vladantrhlik/VT-40/img/2.jpg

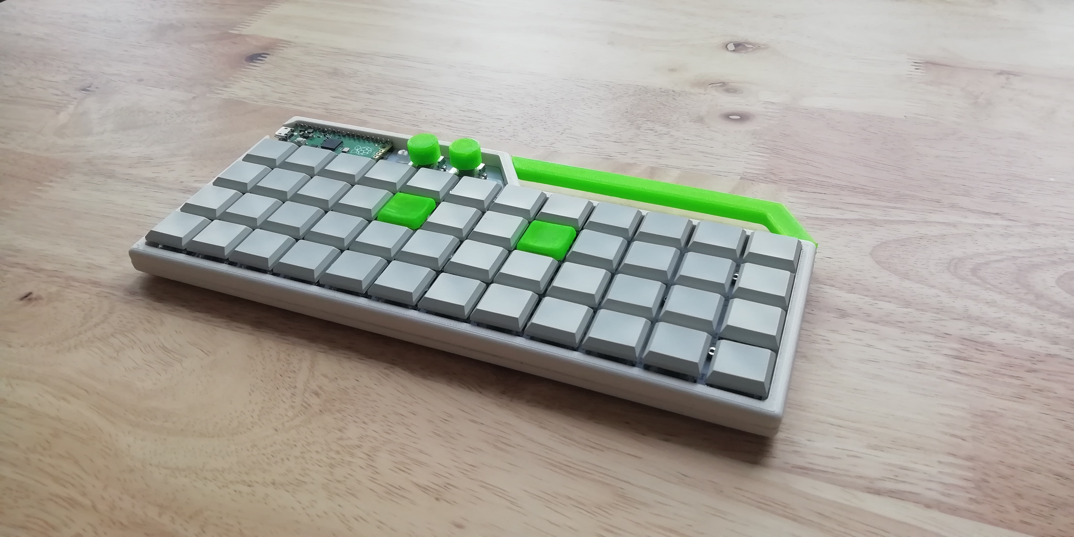
img/2.jpg
