vladantrhlik/VT-40/img/3.jpg

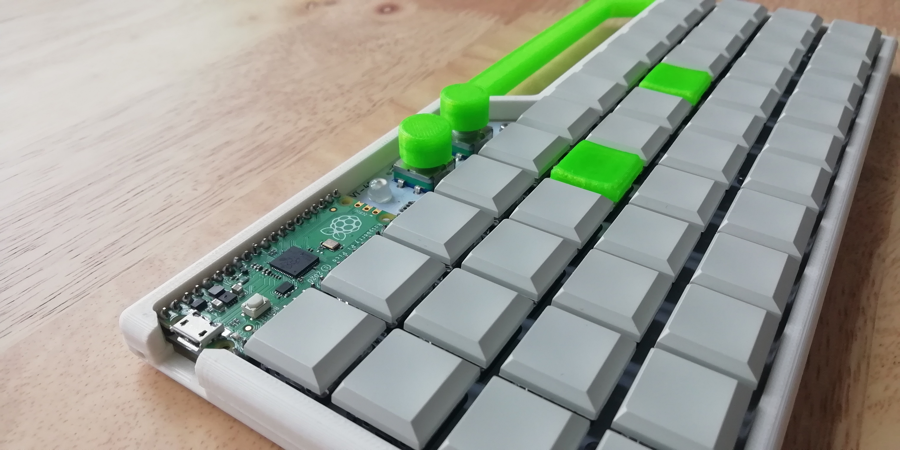
img/3.jpg
