vladantrhlik/VT-40/vt40w/images/IMG20221226110710.jpg

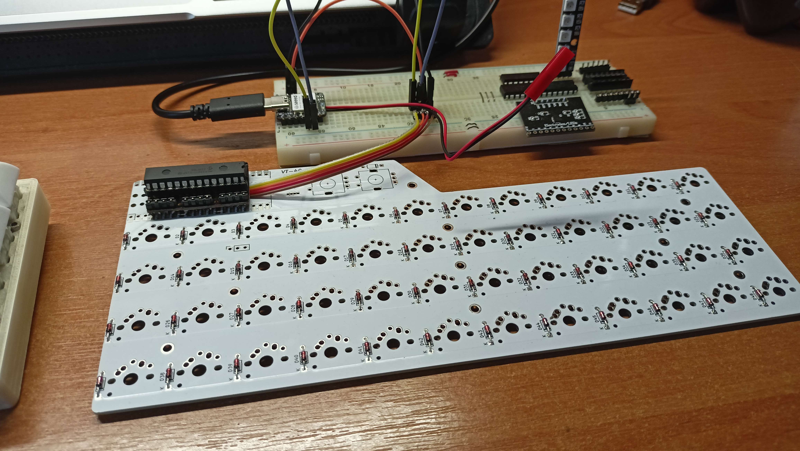
vt40w/images/IMG20221226110710.jpg
